badjeff/leylabella/imgs/p2.jpeg

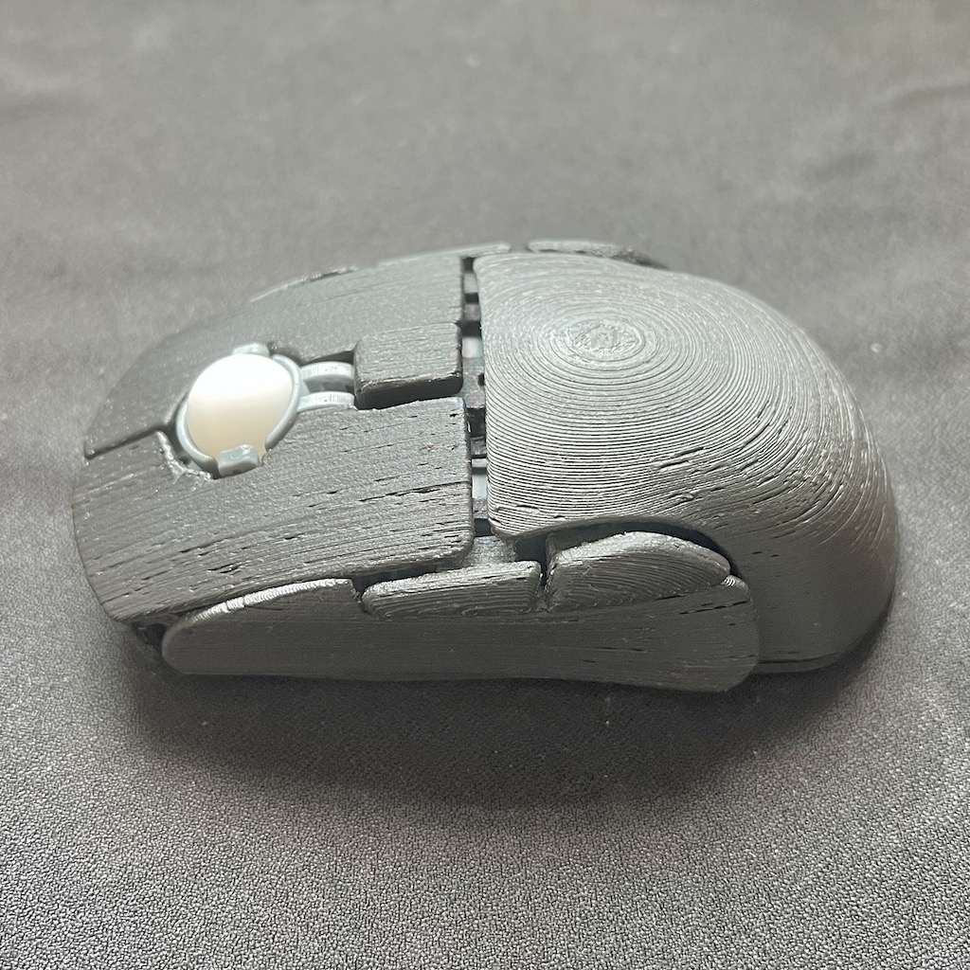
imgs/p2.jpeg
