badjeff/leylabella/imgs/p5.jpeg

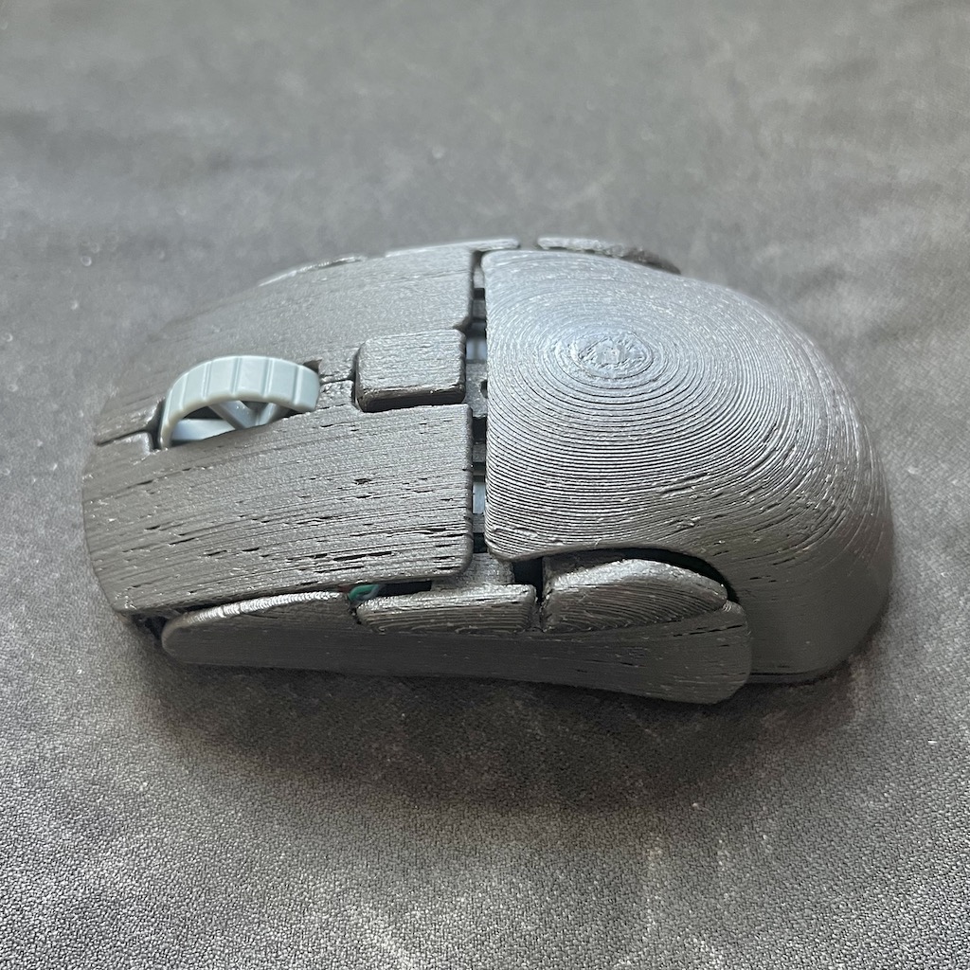
imgs/p5.jpeg
