badjeff/leylabella/STLs/3 - ribs.stl

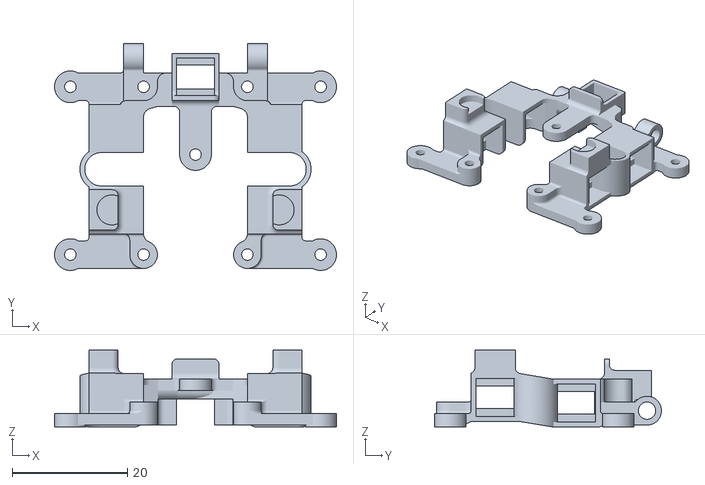
[picture p33: CAD file, 2025-08-09]
STLs/3 - ribs.stl
48.9 x 39.3 x 13.3
